johanmz/MultiFMBerry/hardware/kicad/multifmberry.kicad_sch

## KiCad design hardware/kicad/multifmberry.kicad_sch (2022-02-06)

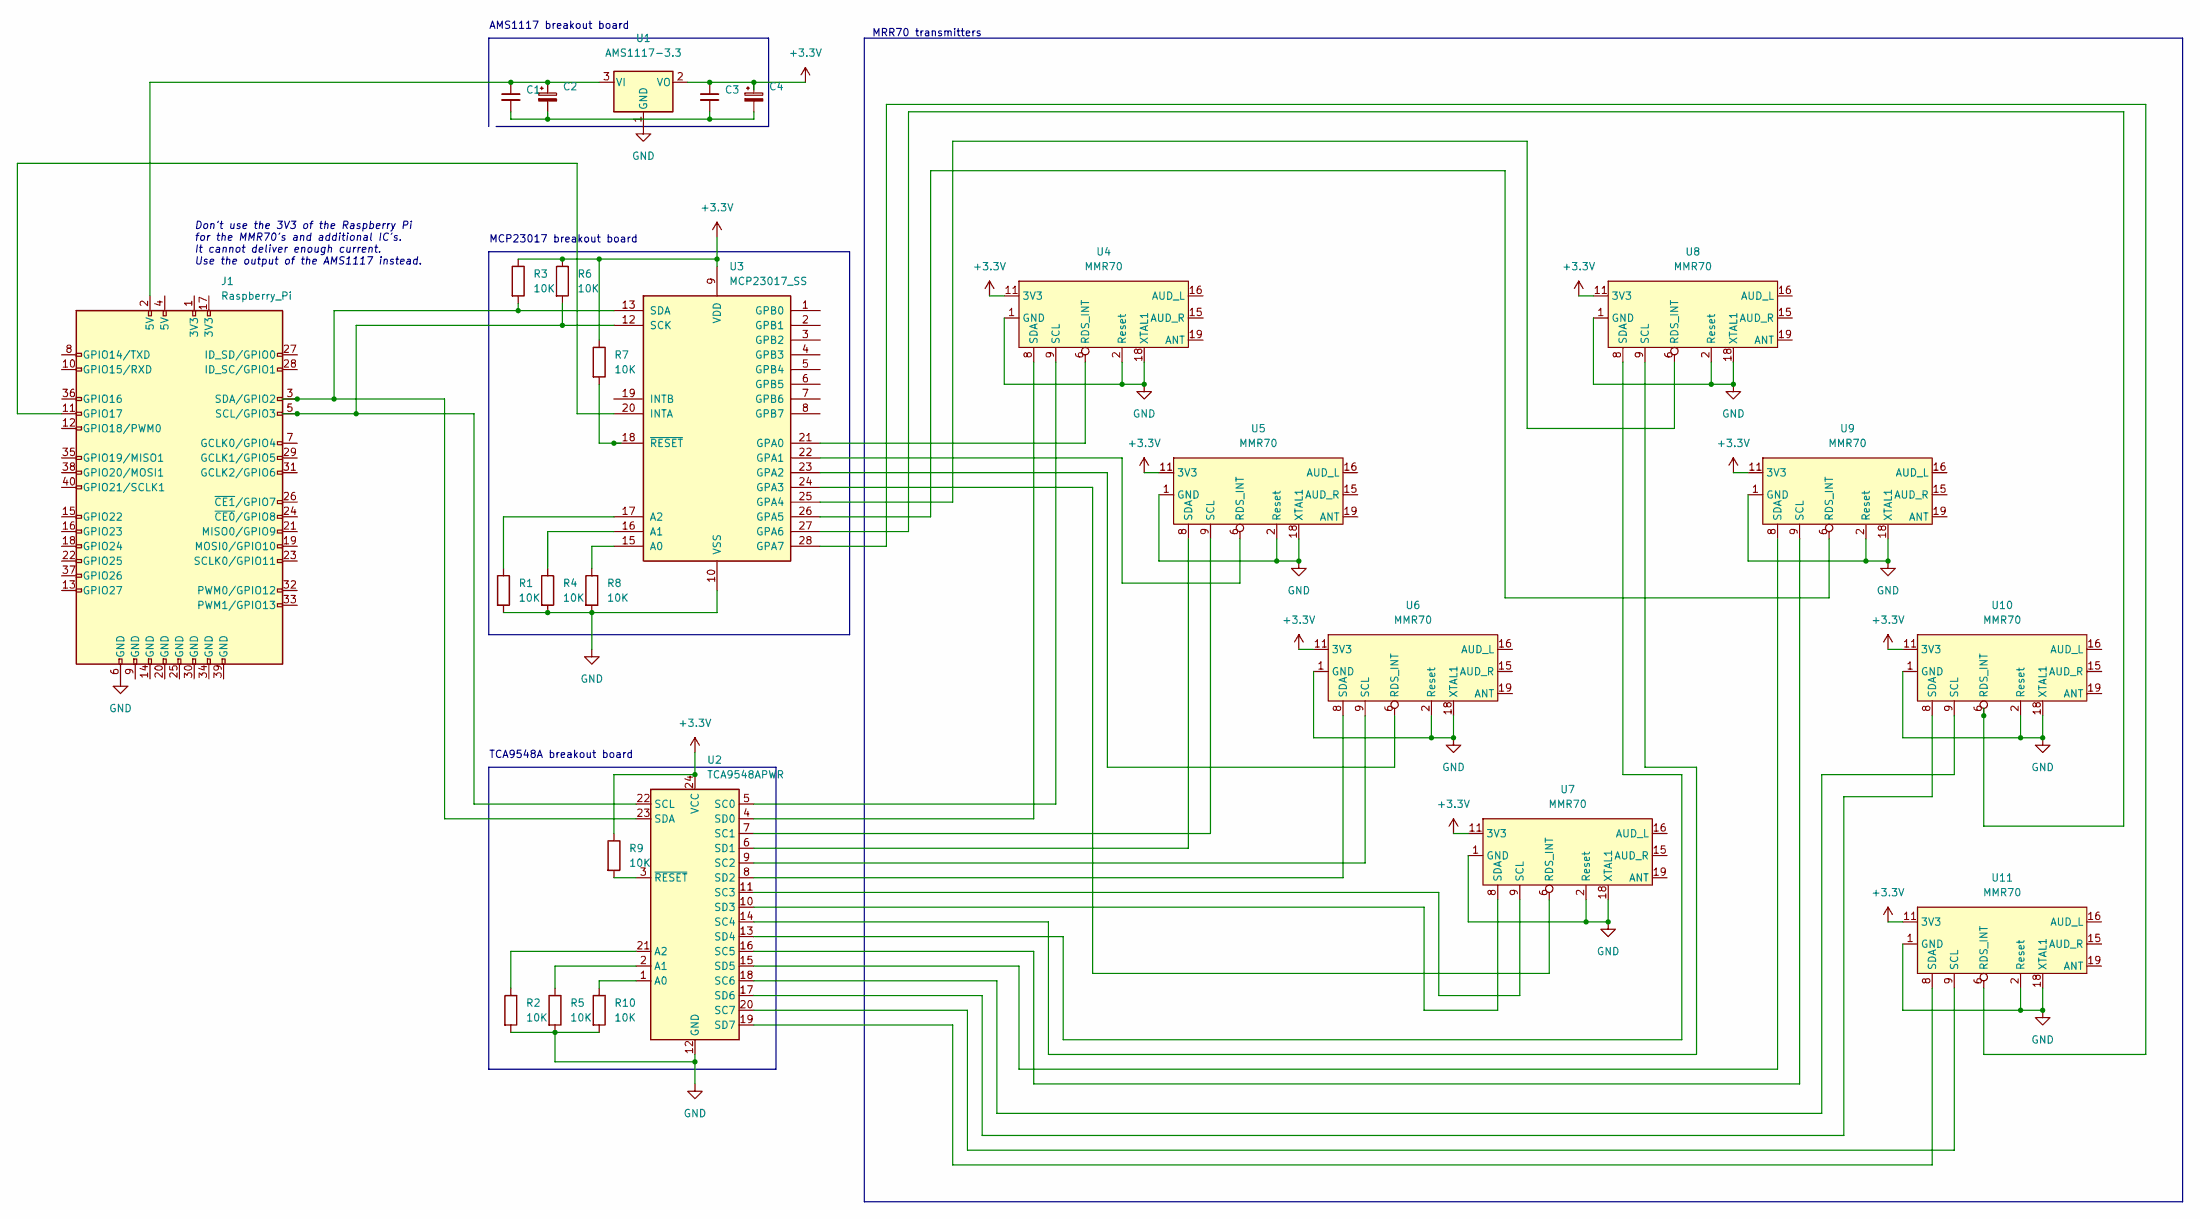
[picture p3: schematic multifmberry.kicad_sch]

Parts:
C1, C2, C3, C4: (no value)
J1: Raspberry_Pi
R1, R2, R3, R4, R5, R6, R7, R8, R9, R10: 10K
U1: AMS1117-3.3; SOT-223-3_TabPin2
U2: TCA9548APWR; TSSOP-24_4.4x7.8mm_P0.65mm
U3: MCP23017_SS; SSOP-28_5.3x10.2mm_P0.65mm
U4, U5, U6, U7, U8, U9, U10, U11: MMR70

Connections:
+3.3V: C3.1, C4.1, R3.1, R6.1, R7.1, R9.1, U1.2 (VO), U2.24 (VCC), U3.9 (VDD), U4.11 (3V3), U5.11 (3V3), U6.11 (3V3), U7.11 (3V3), U8.11 (3V3), U9.11 (3V3), U10.11 (3V3), U11.11 (3V3)
GND: J1.6 (GND), R1.2, R2.2, R4.2, R5.2, R8.2, R10.2, U1.1 (GND), U2.12 (GND), U3.10 (VSS), U4.1 (GND), U4.2 (Reset), U4.18 (XTAL1), U5.1 (GND), U5.2 (Reset), U5.18 (XTAL1), U6.1 (GND), U6.2 (Reset), U6.18 (XTAL1), U7.1 (GND), U7.2 (Reset), U7.18 (XTAL1), U8.1 (GND), U8.2 (Reset), U8.18 (XTAL1), U9.1 (GND), U9.2 (Reset), U9.18 (XTAL1), U10.1 (GND), U10.2 (Reset), U10.18 (XTAL1), U11.1 (GND), U11.2 (Reset), U11.18 (XTAL1)
unnamed: C1.1, C2.1, J1.2 (5V), U1.3 (VI)
unnamed: C1.2, C2.2, C3.2, C4.2
unnamed: J1.3 (SDA/GPIO2), R3.2, U2.23 (SDA), U3.13 (SDA)
unnamed: J1.5 (SCL/GPIO3), R6.2, U2.22 (SCL), U3.12 (SCK)
unnamed: J1.11 (GPIO17), U3.20 (INTA)
unnamed: R1.1, U3.17 (A2)
unnamed: R2.1, U2.21 (A2)
unnamed: R4.1, U3.16 (A1)
unnamed: R5.1, U2.2 (A1)
unnamed: R7.2, U3.18 (~RESET)
unnamed: R8.1, U3.15 (A0)
unnamed: R9.2, U2.3 (~RESET)
unnamed: R10.1, U2.1 (A0)
unnamed: U2.4 (SD0), U4.8 (SDA)
unnamed: U2.5 (SC0), U4.9 (SCL)
unnamed: U2.6 (SD1), U5.8 (SDA)
unnamed: U2.7 (SC1), U5.9 (SCL)
unnamed: U2.8 (SD2), U6.8 (SDA)
unnamed: U2.9 (SC2), U6.9 (SCL)
unnamed: U2.10 (SD3), U7.8 (SDA)
unnamed: U2.11 (SC3), U7.9 (SCL)
unnamed: U2.13 (SD4), U8.8 (SDA)
unnamed: U2.14 (SC4), U8.9 (SCL)
unnamed: U2.15 (SD5), U9.8 (SDA)
unnamed: U2.16 (SC5), U9.9 (SCL)
unnamed: U3.21 (GPA0), U4.6 (RDS_INT)
unnamed: U3.22 (GPA1), U5.6 (RDS_INT)
unnamed: U3.23 (GPA2), U6.6 (RDS_INT)
unnamed: U3.24 (GPA3), U7.6 (RDS_INT)
unnamed: U3.25 (GPA4), U8.6 (RDS_INT)
unnamed: U3.26 (GPA5), U9.6 (RDS_INT)
unnamed: U3.27 (GPA6), U10.6 (RDS_INT)
unnamed: U2.17 (SD6), U10.8 (SDA)
unnamed: U2.18 (SC6), U10.9 (SCL)
unnamed: U3.28 (GPA7), U11.6 (RDS_INT)
unnamed: U2.19 (SD7), U11.8 (SDA)
unnamed: U2.20 (SC7), U11.9 (SCL)

Notes on the sheet:
TCA9548A breakout board
AMS1117 breakout board
MCP23017 breakout board
MRR70 transmitters
Don't use the 3V3 of the Raspberry Pi for the MMR70's and additional IC's. It cannot deliver enough current. Use the output of the AMS1117 instead.
