johanmz/MultiFMBerry/mcp23017.c

/*
	FMBerry - an cheap and easy way of transmitting music with your Pi.
	Copyright (C) 2021      by Johan Muizelaar - modifications for multiple fm transmitters - (https://github.com/johanmz)

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
    You should have received a copy of the GNU General Public License
    along with this program.  If not, see <http://www.gnu.org/licenses/>.
*/
#include <stdio.h>
#include <unistd.h>
#include "i2c.h"
#include "defs.h"
#include "fmberryd.h"

static int i2cbus = -1;
static int address;

// initialise i2c bus for IOexpander(s) used to read the RDS_INT signal from the transmitters
// mcp23017 is by default already in paired (BANK=0) mode and GPIOA/B is by default already in input mode. Which is what we need :-)
int mcp23017_init_i2c (uint8_t bus)
{
    for (int j=0; j<MAXIOEXPANDERS; j++) {
        address = IOexpander[j].address;
        if (address) {
            IOexpander[j].i2cbus=i2c_init(bus, address);
            if (IOexpander[j].i2cbus == -1) 
                return -1;
        }
        else   
            break;
    }
    return 0;
}

// read which transmitter(s) have RDS_INT set, i.e. are ready to receive the next RDS block
uint16_t mcp23017_read_trs_rdsstatus (int index)
{
    char buf[2];
    i2cbus = IOexpander[index].i2cbus;
    buf[0]=0x12; // pointer to GPIOA register
									
	// set mcp20137 pointer to GPIOA
    if ((write(i2cbus, buf, 1)) != 1)
		return -1;
    // and read the values of both GPIOA and GPIOB
    if (read(i2cbus, buf, 2) != 2)
        return -1;
    else
        return buf[0]+(buf[1]<<8);
}

// setup the interrupt registers for the mcp23017, we need this to pass the RDS_INT for the transmitters to the raspberry pi
int mcp23017_init_INT (int nr_transmitters)
{
 
     // build up the GPINTEN register for the ports with a MMR70 connected, for each mcp23017
    int IOexpanderport;
    uint16_t GPINTEN=0;

    for (int k=0; k<nr_transmitters; k++) {
        if (mmr70[k].rds) {
            IOexpanderport=mmr70[k].IOexpanderport;
            GPINTEN = IOexpander[mmr70[k].IOexpanderindex].GPINTEN;
            GPINTEN |= 1 << IOexpanderport;
            IOexpander[mmr70[k].IOexpanderindex].GPINTEN= GPINTEN;
        }
    } 
    // initalise each mcp23017 to handle the interrupts from the transmitters
    // enable only connected ports to trigger an interrupt, when RDSINT of transmitter goes low
	char buf[8];
    
    for (int j=0; j<MAXIOEXPANDERS; j++) {
        if (IOexpander[j].address) {
            GPINTEN = IOexpander[j].GPINTEN;
    	    buf[0] = 0x04;	            // start address for writing which ports 		
	        buf[1] = GPINTEN & 0xFF;    // enable the interrupts for the mcp20137 io ports where a transmitter is connected to
	        buf[2] = (GPINTEN & 0xFF00) >> 8;
            buf[3] = 0b11111111;        // DEFVAL, trigger on low 
            buf[4] = 0b11111111;
            buf[5] = 0b11111111;        // INTCON, trigger on compare to default value
            buf[6] = 0b11111111;
            buf[7] = 0b01000000;        // IOCON, set interrupt in mirror mode
    	    if ((write(IOexpander[j].i2cbus, buf, 8)) != 8) {
	    	    return -1;
	        }
            uint16_t result;
            result = mcp23017_read_trs_rdsstatus (j); // read gpio otherwise interrupts might not start
        }
        else
            break;
    }
    return 0;
}
